Elecrow-RD/All-in-one-Starter-Kit-for-Arduino-Nano-R4/lesson_code/12_6-Axis/12_6-Axis.ino

#include <Arduino_LSM6DS3.h>
#include <MadgwickAHRS.h>

#define SAMPLE_RATE 10  // in Hz

Madgwick filter;  // Madgwick algorithm for roll, pitch, and yaw calculations

// Prints IMU values.
void printValues() {
   char buffer[8];    // string buffer for use with dtostrf() function
   float ax, ay, az;  // accelerometer values
   float gx, gy, gz;  // gyroscope values

   if (IMU.accelerationAvailable() && IMU.gyroscopeAvailable()
      && IMU.readAcceleration(ax, ay, az) && IMU.readGyroscope(gx, gy, gz)) {
      Serial.print("ax = ");  Serial.print(dtostrf(ax, 4, 1, buffer));  Serial.print(" g, ");
      Serial.print("ay = ");  Serial.print(dtostrf(ay, 4, 1, buffer));  Serial.print(" g, ");
      Serial.print("az = ");  Serial.print(dtostrf(az, 4, 1, buffer));  Serial.print(" g, ");
      Serial.print("gx = ");  Serial.print(dtostrf(gx, 7, 1, buffer));  Serial.print(" °/s, ");
      Serial.print("gy = ");  Serial.print(dtostrf(gy, 7, 1, buffer));  Serial.print(" °/s, ");
      Serial.print("gz = ");  Serial.print(dtostrf(gz, 7, 1, buffer));  Serial.println(" °/s");
   }
}

void printRotationAngles() {
   char buffer[5];    // string buffer for use with dtostrf() function
   float ax, ay, az;  // accelerometer values
   float gx, gy, gz;  // gyroscope values

   if (IMU.accelerationAvailable() && IMU.gyroscopeAvailable()
      && IMU.readAcceleration(ax, ay, az) && IMU.readGyroscope(gx, gy, gz)) {
      filter.updateIMU(gx, gy, gz, ax, ay, az);  // update roll, pitch, and yaw values

      // Print rotation angles
      Serial.print("Roll = ");  Serial.print(dtostrf(filter.getRoll(), 4, 0, buffer)); Serial.print(" °, ");
      Serial.print("Pitch = ");  Serial.print(dtostrf(filter.getPitch(), 4, 0, buffer)); Serial.print(" °, ");
      Serial.print("Yaw = ");  Serial.print(dtostrf(filter.getYaw(), 4, 0, buffer)); Serial.println(" °");
   }
}

void setup() {
   Serial.begin(115200);  // initialize serial bus (Serial Monitor)
   IMU.begin();
   filter.begin(SAMPLE_RATE);  // initialize Madgwick filter
}

void loop() {
   static unsigned long previousTime = millis();
   unsigned long currentTime = millis();
   if (currentTime - previousTime >= 1000/SAMPLE_RATE) {
      printValues();
      printRotationAngles();
      previousTime = millis();
   }
}
