Elecrow-RD/All-in-one-Starter-Kit-for-Arduino-Nano-R4/lesson_code/13_Light_Sensor/13_Light_Sensor.ino

/*******************Light Sensor*******************/
#include <BH1750.h>            // Include BH1750 light sensor library
BH1750 lightMeter(0x5c);      // Create sensor object with I2C address 0x5c

float lux;                    // Stores measured light intensity in lux
int LedPin = 5;              // LED control pin (PWM capable)

void setup() {
  // Initialize serial communication for debugging
  Serial.begin(115200);   
  
  // Initialize I2C communication (required for BH1750)
  Wire.begin();

  // Initialize BH1750 sensor in continuous high-resolution mode (1 lux precision)
  lightMeter.begin(BH1750::CONTINUOUS_HIGH_RES_MODE, 0x5c, &Wire);
  // Configure LED pin as output
  pinMode(LedPin, OUTPUT);
}

void loop() {
  // Check if light measurement is ready (blocking wait if true)
    lux = lightMeter.readLightLevel();  // Read light level in lux
    Serial.print("[-] Light: [");
    Serial.print(lux);
    Serial.println("] lx");             // Print light level to serial monitor

  if (lux <= 100)
    digitalWrite(LedPin, HIGH);
  else
    digitalWrite(LedPin, LOW);
}
